HakoForge/HakoCore/Accessories/Case Subparts/AirBlock Ends Left.stl

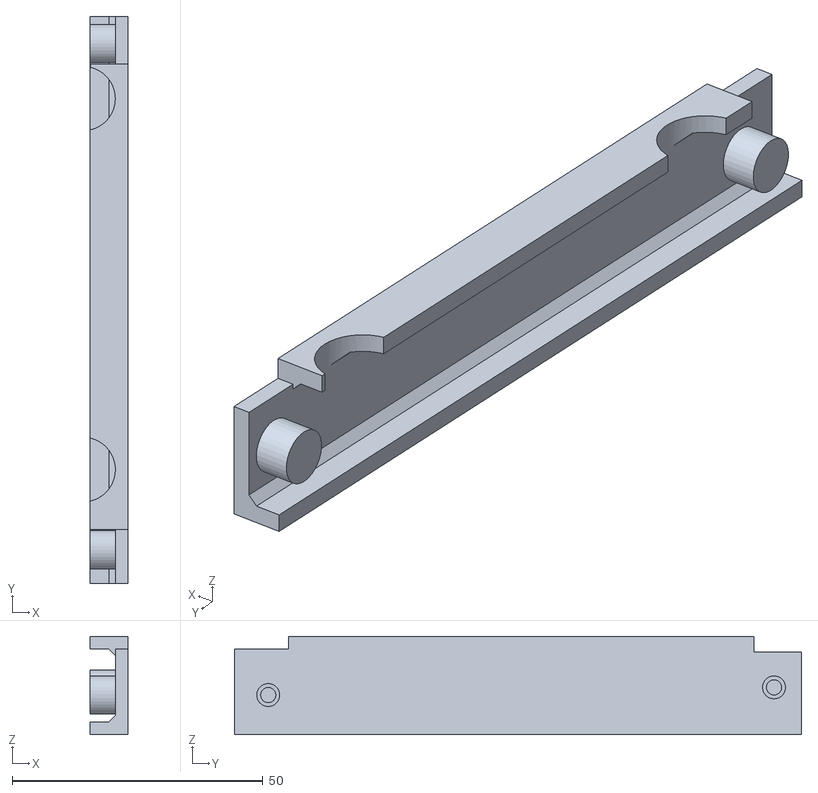
[picture p16: CAD file, 2025-04-07]
Accessories/Case Subparts/AirBlock Ends Left.stl
7.62 x 113.1 x 19.6
