HakoForge/HakoCore/Accessories/Other/PCie_Card_Support v1.4.stl

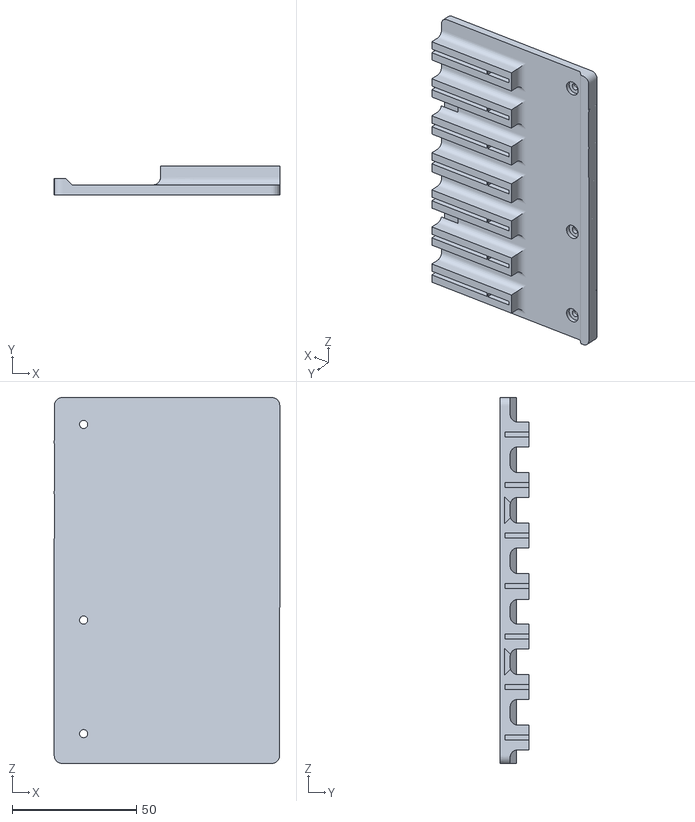
[picture p18: CAD file, 2026-10-05]
Accessories/Other/PCie_Card_Support v1.4.stl
90.8 x 11.5 x 147.3
