HakoForge/HakoCore/Accessories/Fan Mounts/Fan_Bracket_120_PCIe.stl

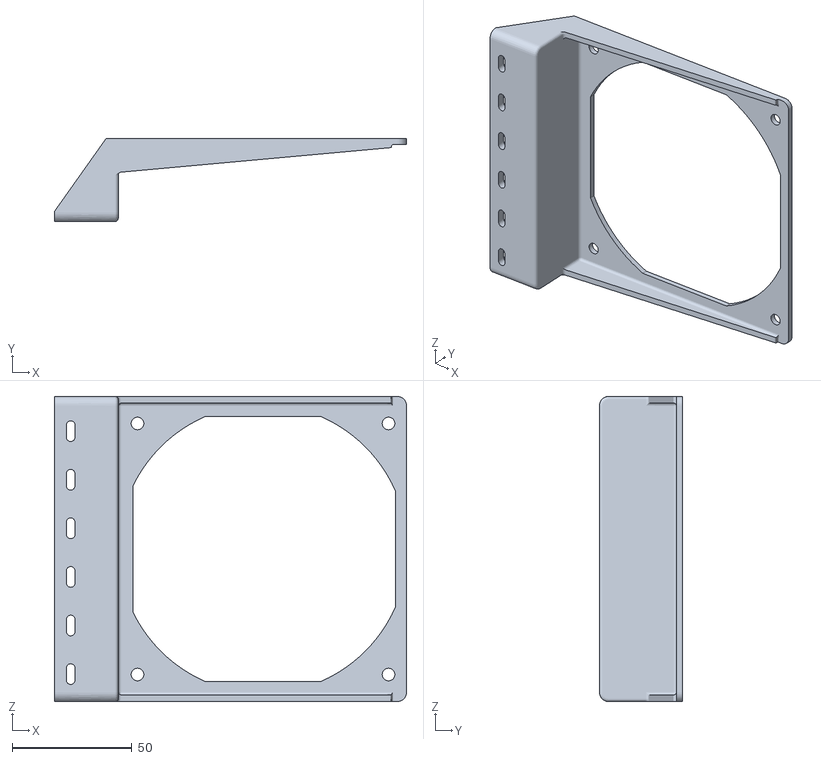
[picture p19: CAD file, 2025-04-07]
Accessories/Fan Mounts/Fan_Bracket_120_PCIe.stl
147.2 x 34.7 x 127.6
