HakoForge/HakoCore/Accessories/Other/PCie_Card_Support v1.4_feet.stl

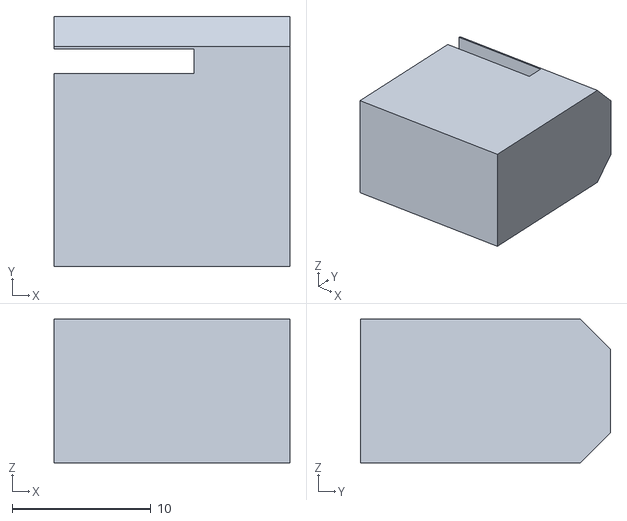
[picture p20: CAD file, 2026-10-05]
Accessories/Other/PCie_Card_Support v1.4_feet.stl
17.0 x 18.0 x 10.4
