HakoForge/HakoCore/Cages/2x2 HDD-SSD Small Cage/Cage 2x2 rev2.step

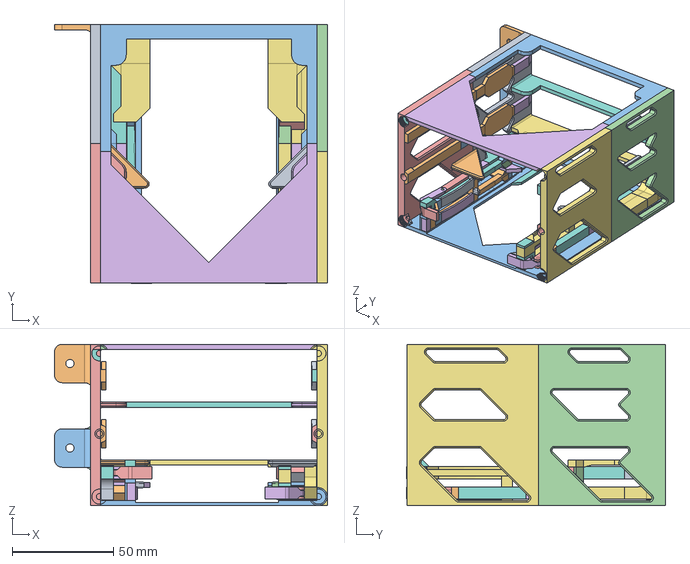
[picture p21: CAD file, 2025-04-07]
Cages/2x2 HDD-SSD Small Cage/Cage 2x2 rev2.step
135.1 x 128.0 x 79.9 mm
Drive Cage 4 v3 Rev.6 v1
Drive Cage 4 v3 Rev.6 v1 (1)
