HakoForge/HakoCore/Case/Core Mini/PSU_Bracket.step

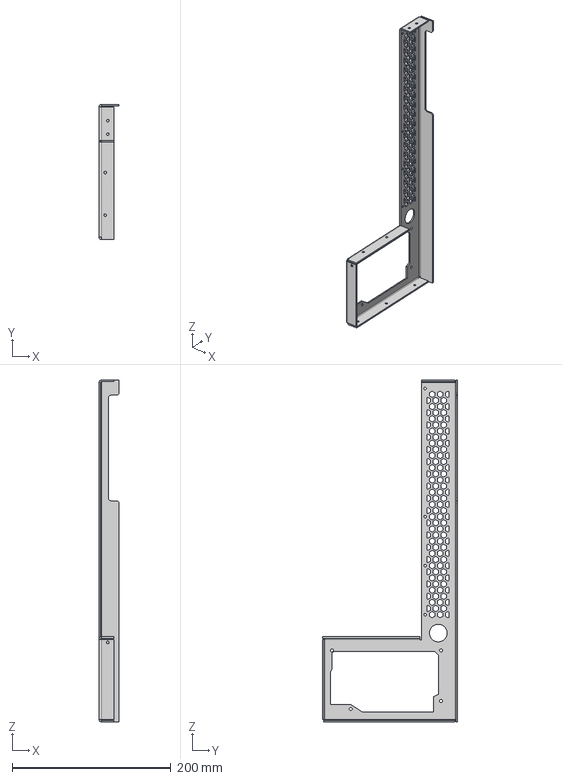
[picture p22: CAD file, 2025-04-07]
Case/Core Mini/PSU_Bracket.step
25.4 x 170.7 x 431.5 mm
