HakoForge/HakoCore/Case/Core/Hako-Core Rev1.step

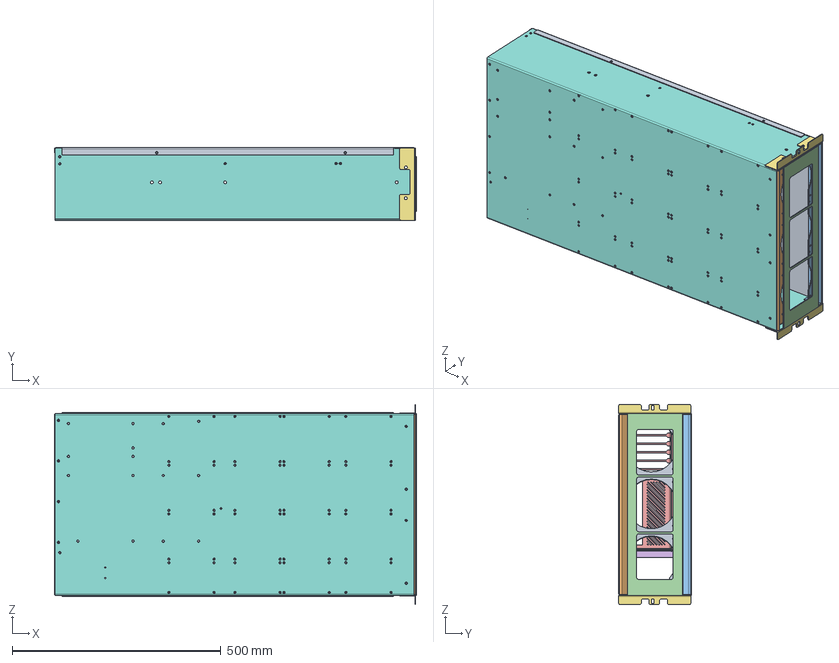
[picture p23: CAD file, 2025-04-07]
Case/Core/Hako-Core Rev1.step
867.6 x 173.9 x 479.6 mm
Rear IO Reccessed Copy (1)
Rear IO Reccessed Copy (1)_1
Rear IO Reccessed Copy (1)_2
Front Panel Airflow
Rear IO Reccessed Copy (1)_3
Rear IO Reccessed Copy (1)_4
Rack Ears
Rack Ears_1
Server Chassis Bottom
Lid
Rear IO Reccessed Copy (1)_5
