HakoForge/HakoCore/Accessories/Other/SSD Removal Tool v2.4.stl

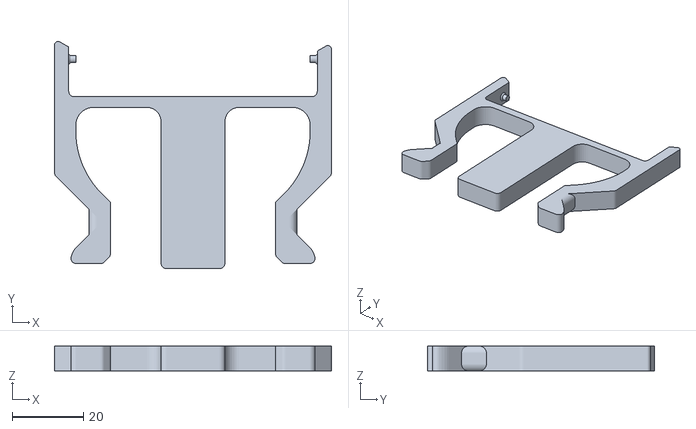
[picture p24: CAD file, 2026-10-05]
Accessories/Other/SSD Removal Tool v2.4.stl
78.0 x 64.0 x 7.00
