HakoForge/HakoCore/Case/Core/Cage_Mount_Sm.step

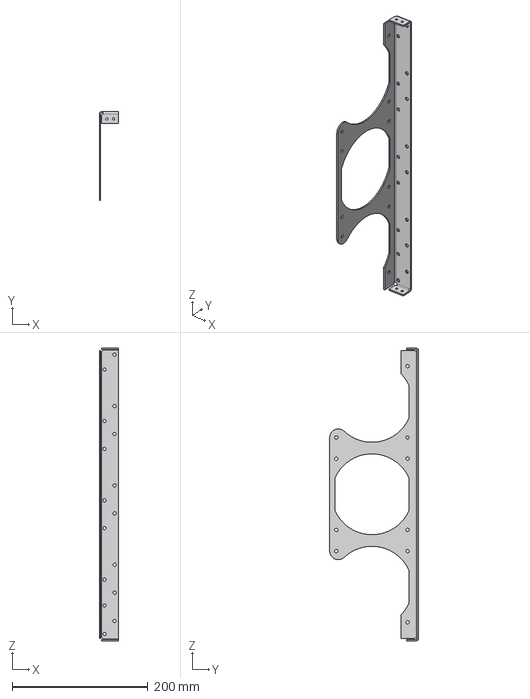
[picture p25: CAD file, 2025-04-07]
Case/Core/Cage_Mount_Sm.step
28.7 x 130.6 x 431.5 mm
