HakoForge/HakoCore/Accessories/Fan Mounts/Fan_Bracket_80_55.stl

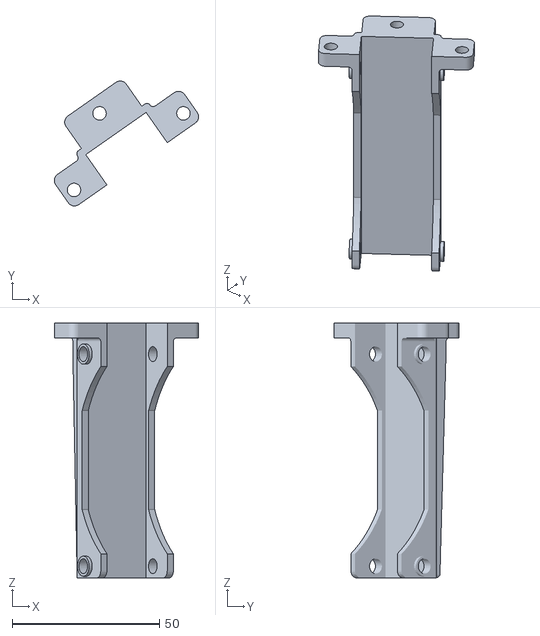
[picture p26: CAD file, 2025-04-07]
Accessories/Fan Mounts/Fan_Bracket_80_55.stl
49.0 x 42.4 x 86.6
