HakoForge/HakoCore/Accessories/Other/Cable_Management_B.step

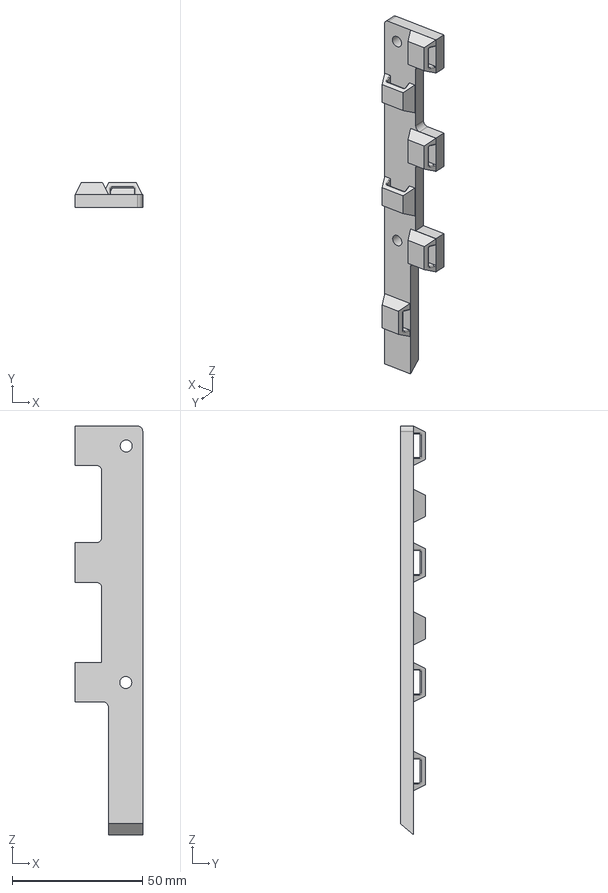
[picture p27: CAD file, 2026-10-05]
Accessories/Other/Cable_Management_B.step
25.9 x 9.65 x 156.8 mm
