HakoForge/HakoCore/Case/Core/34_Cage_Mount_Bg.step

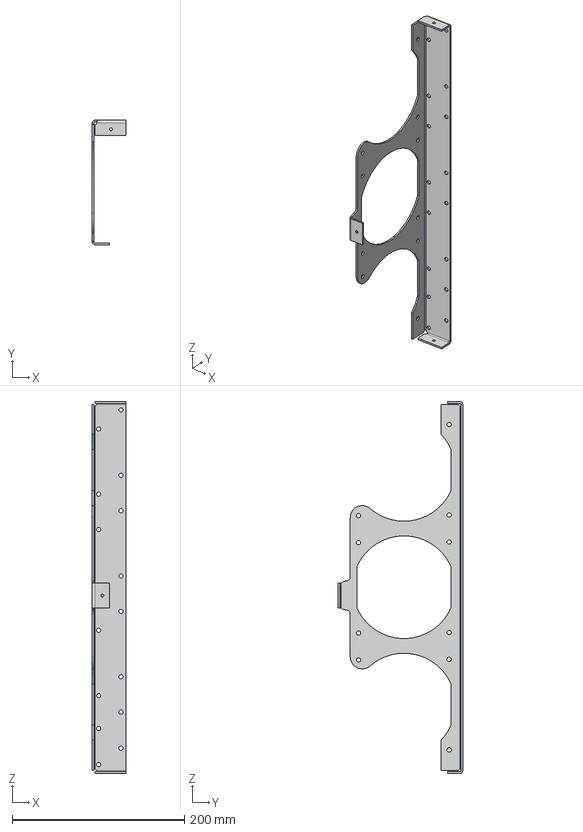
[picture p28: CAD file, 2025-04-07]
Case/Core/34_Cage_Mount_Bg.step
39.0 x 144.6 x 431.5 mm
