HakoForge/HakoCore/Accessories/Fan Mounts/Fan_Bracket_Spacer_90_5_v2.stl

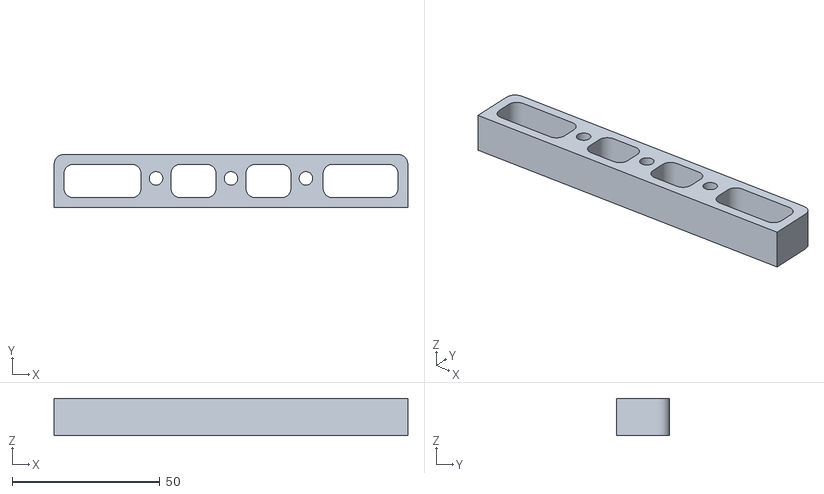
[picture p29: CAD file, 2025-04-07]
Accessories/Fan Mounts/Fan_Bracket_Spacer_90_5_v2.stl
120.0 x 18.1 x 12.7
