HakoForge/HakoCore/Accessories/Other/2.5 15mm SSD Adapter v0.3.stl

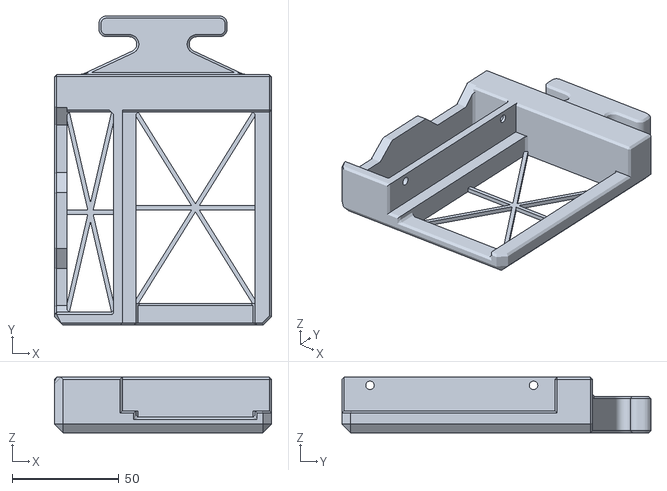
[picture p30: CAD file, 2026-10-05]
Accessories/Other/2.5 15mm SSD Adapter v0.3.stl
101.6 x 144.6 x 26.0
