HakoForge/HakoCore/Case/Core Mini/Hako-Core Mini Rev1.step

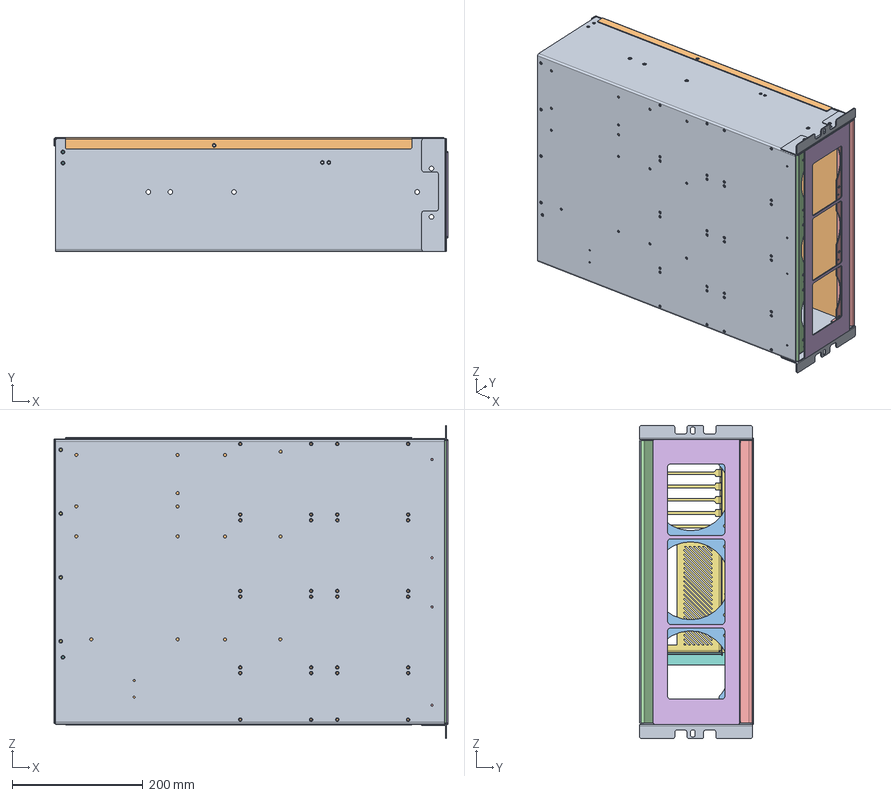
[picture p31: CAD file, 2025-04-07]
Case/Core Mini/Hako-Core Mini Rev1.step
602.5 x 174.3 x 479.2 mm
Server Chassis Bottom
Lid
Rear IO Reccessed Copy (1)
Rear IO Reccessed Copy (1)_1
Rear IO Reccessed Copy (1)_2
Front Panel Airflow
Rear IO Reccessed Copy (1)_3
Rear IO Reccessed Copy (1)_4
Rack Ears
Rack Ears_1
