HakoForge/HakoCore/Case/Core Mini/24_Chassis.step

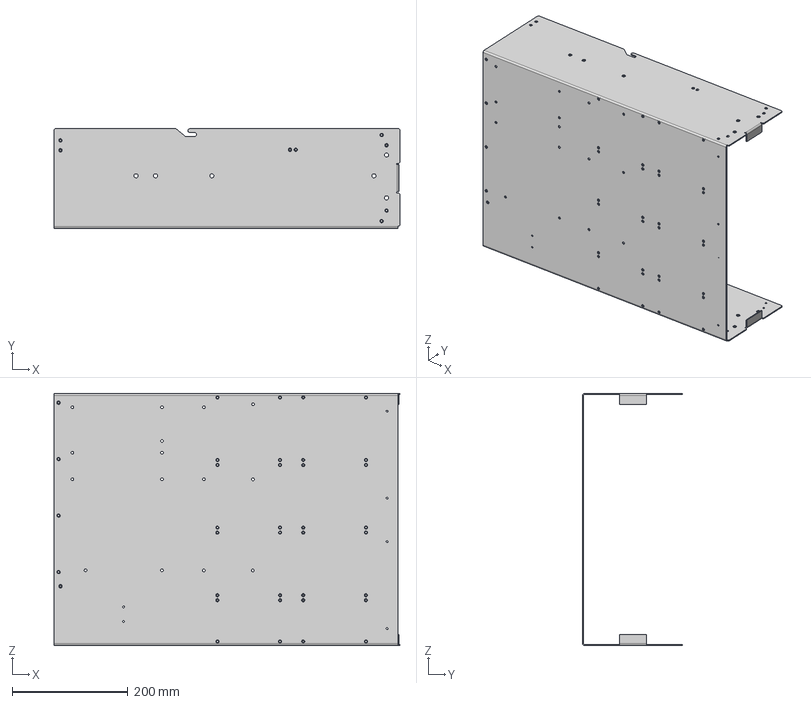
[picture p33: CAD file, 2025-04-07]
Case/Core Mini/24_Chassis.step
597.9 x 172.7 x 435.6 mm
