HakoForge/HakoCore/Accessories/Fan Mounts/Fan_Bracket_120_PCIe_Mirrored.stl

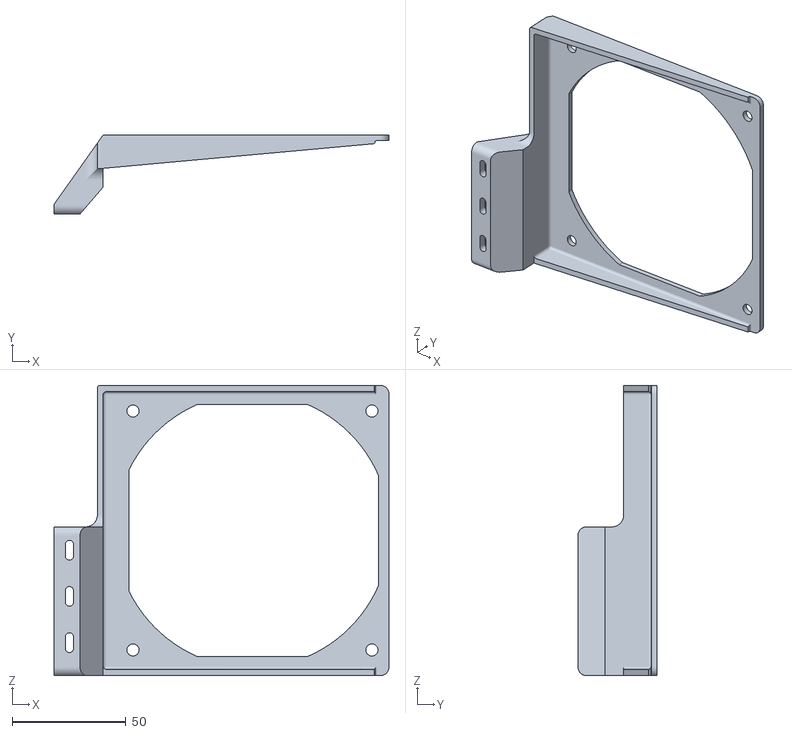
[picture p34: CAD file, 2025-04-07]
Accessories/Fan Mounts/Fan_Bracket_120_PCIe_Mirrored.stl
147.2 x 34.7 x 127.6
