HakoForge/HakoCore/Case/Core/34_Chassis.step

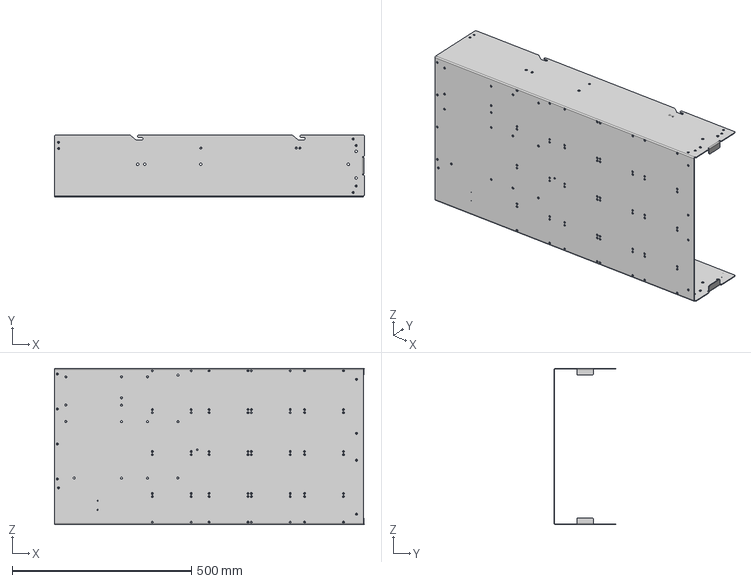
[picture p35: CAD file, 2025-04-07]
Case/Core/34_Chassis.step
863.6 x 172.7 x 435.6 mm
