HakoForge/HakoCore/Accessories/Fan Mounts/Fan_Bracket_92_55.stl

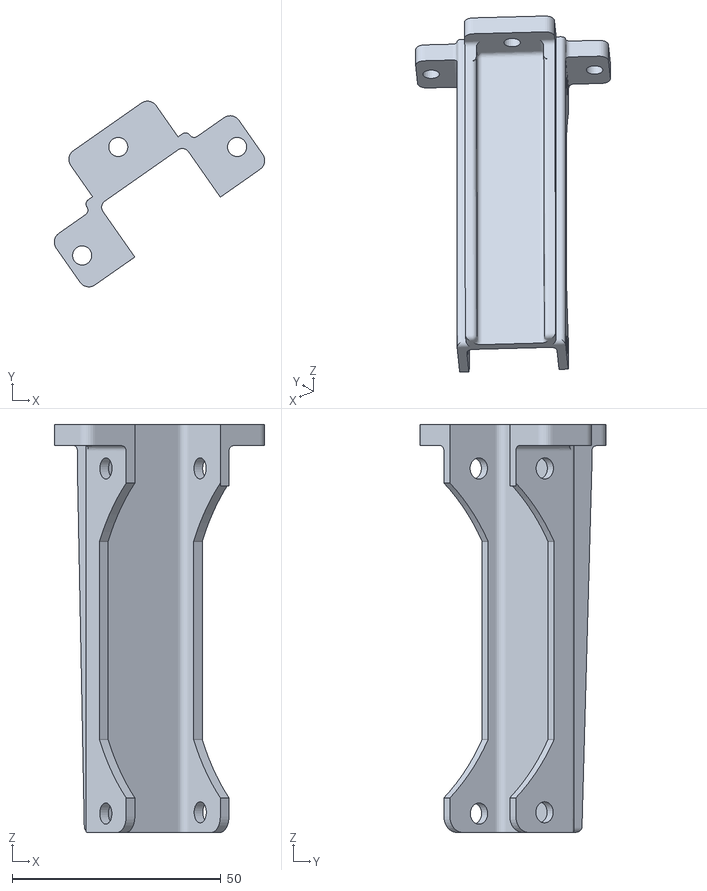
[picture p36: CAD file, 2025-04-07]
Accessories/Fan Mounts/Fan_Bracket_92_55.stl
50.4 x 44.5 x 97.8
