HakoForge/HakoCore/Case/Core Mini/24_Lid.step

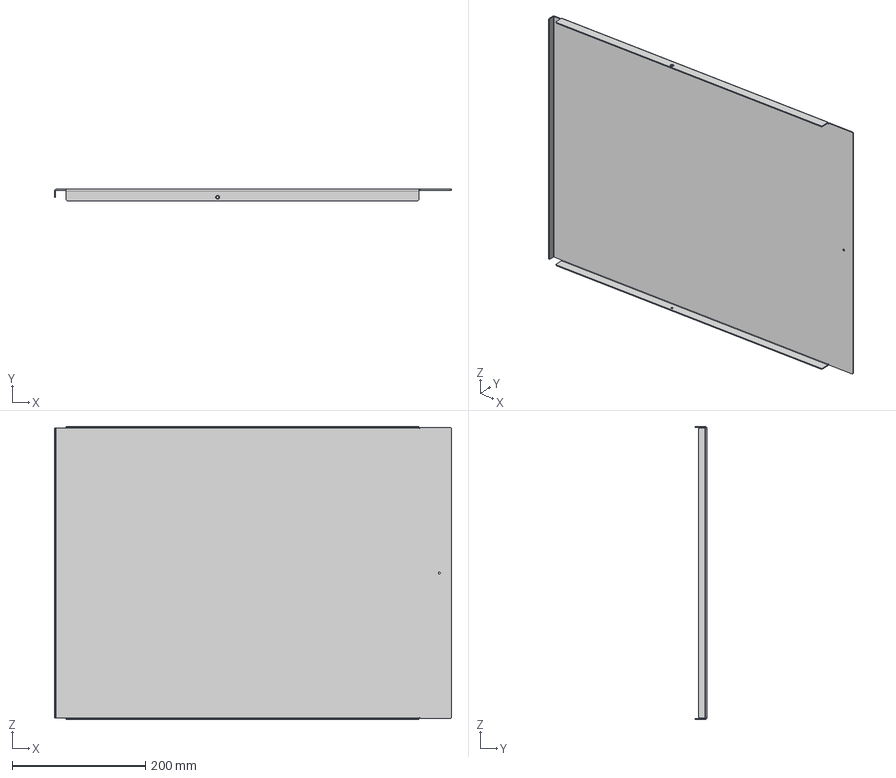
[picture p37: CAD file, 2025-04-07]
Case/Core Mini/24_Lid.step
596.2 x 17.5 x 440.1 mm
