HakoForge/HakoCore/Case/Core/34_Lid.step

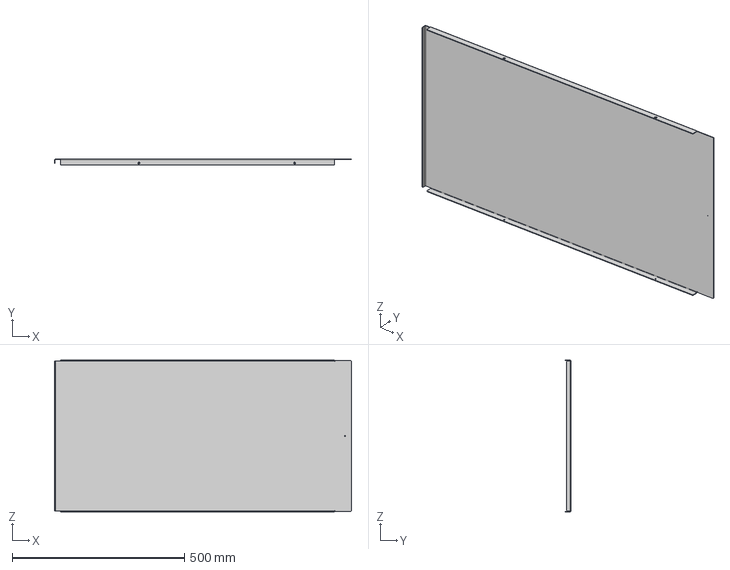
[picture p38: CAD file, 2025-04-07]
Case/Core/34_Lid.step
861.9 x 17.5 x 440.1 mm
