HakoForge/HakoCore/Accessories/Fan Mounts/Fan_Bracket_Spacer_55_10.stl

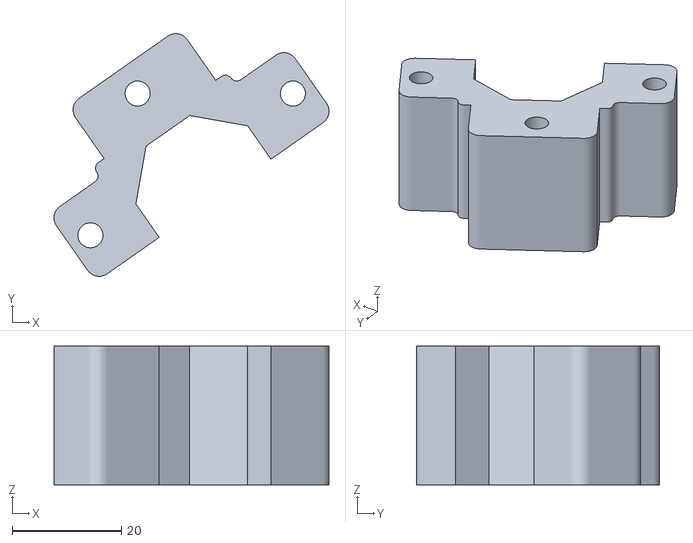
[picture p39: CAD file, 2025-04-07]
Accessories/Fan Mounts/Fan_Bracket_Spacer_55_10.stl
50.4 x 44.5 x 25.4
